NASCENCE/mecobo/EMServer/bin/77ac0f1f-8d66-4bb2-870d-c3d88853328c.pdf

# PIN15

# PIN14

# PIN13

# PIN12

# PIN11

# PIN10

# PIN09

# PIN08

# PIN07

# PIN06

# PIN05

# PIN04

# PIN02

# PIN01

# PIN00

CONSTANT 1V

CONSTANT 1V

CONSTANT 1V

CONSTANT 1V

CONSTANT 1V

CONSTANT 1V

CONSTANT 1V

CONSTANT 1V

CONSTANT 1V

CONSTANT 1V

CONSTANT 1V

CONSTANT 1V

CONSTANT 1V

CONSTANT 1V

CONSTANT 1V

CONSTANT 1V

CONSTANT 1V

CONSTANT 1V

CONSTANT 1V

CONSTANT 1V

CONSTANT 1V

CONSTANT 1V

CONSTANT 1V

CONSTANT 1V

CONSTANT 1V

CONSTANT 1V

CONSTANT 1V

CONSTANT 1V

CONSTANT 1V

CONSTANT 1V

CONSTANT 44V

CONSTANT 44V

CONSTANT 44V

CONSTANT 44V

CONSTANT 44V

CONSTANT 44V

CONSTANT 44V

CONSTANT 44V

CONSTANT 44V

CONSTANT 44V

CONSTANT 44V

CONSTANT 44V

CONSTANT 44V

CONSTANT 44V

CONSTANT 44V

CONSTANT 156V

CONSTANT 156V

CONSTANT 156V

CONSTANT 156V

CONSTANT 156V

CONSTANT 156V

CONSTANT 156V

CONSTANT 156V

CONSTANT 156V

CONSTANT 156V

CONSTANT 156V

CONSTANT 156V

CONSTANT 156V

CONSTANT 156V

CONSTANT 156V

CONSTANT 68V

CONSTANT 68V

CONSTANT 68V

CONSTANT 68V

CONSTANT 68V

CONSTANT 68V

CONSTANT 68V

CONSTANT 68V

CONSTANT 68V

CONSTANT 68V

CONSTANT 68V

CONSTANT 68V

CONSTANT 68V

CONSTANT 68V

CONSTANT 68V

CONSTANT 34V

CONSTANT 34V

CONSTANT 34V

CONSTANT 34V

CONSTANT 34V

CONSTANT 34V

CONSTANT 34V

CONSTANT 34V

CONSTANT 34V

CONSTANT 34V

CONSTANT 34V

CONSTANT 34V

CONSTANT 34V

CONSTANT 34V

CONSTANT 34V

CONSTANT 4V

CONSTANT 4V

CONSTANT 4V

CONSTANT 4V

CONSTANT 4V

CONSTANT 4V

CONSTANT 4V

CONSTANT 4V

CONSTANT 4V

CONSTANT 4V

CONSTANT 4V

CONSTANT 4V

CONSTANT 4V

CONSTANT 4V

CONSTANT 4V

RECORD

RECORD

RECORD

RECORD

RECORD

RECORD

RECORD

RECORD

RECORD

RECORD

RECORD

RECORD

RECORD

RECORD

RECORD
