NASCENCE/mecobo/EMServer/bin/7c396e15-6470-4e9b-a8e9-4cceba5d37cf.pdf

# PIN15

# PIN14

# PIN13

# PIN12

# PIN11

# PIN10

# PIN09

# PIN08

# PIN07

# PIN06

# PIN05

# PIN04

# PIN02

# PIN01

# PIN00

CONSTANT 255V

CONSTANT 255V

CONSTANT 255V

CONSTANT 255V

CONSTANT 255V

CONSTANT 255V

CONSTANT 255V

CONSTANT 255V

CONSTANT 255V

CONSTANT 255V

CONSTANT 255V

CONSTANT 255V

CONSTANT 255V

CONSTANT 255V

CONSTANT 255V

CONSTANT 255V

CONSTANT 255V

CONSTANT 255V

CONSTANT 255V

CONSTANT 255V

CONSTANT 255V

CONSTANT 255V

CONSTANT 255V

CONSTANT 255V

CONSTANT 255V

CONSTANT 255V

CONSTANT 255V

CONSTANT 255V

CONSTANT 255V

CONSTANT 255V

CONSTANT 53V

CONSTANT 53V

CONSTANT 53V

CONSTANT 53V

CONSTANT 53V

CONSTANT 53V

CONSTANT 53V

CONSTANT 53V

CONSTANT 53V

CONSTANT 53V

CONSTANT 53V

CONSTANT 53V

CONSTANT 53V

CONSTANT 53V

CONSTANT 53V

CONSTANT 8V

CONSTANT 8V

CONSTANT 8V

CONSTANT 8V

CONSTANT 8V

CONSTANT 8V

CONSTANT 8V

CONSTANT 8V

CONSTANT 8V

CONSTANT 8V

CONSTANT 8V

CONSTANT 8V

CONSTANT 8V

CONSTANT 8V

CONSTANT 8V

CONSTANT 240V

CONSTANT 240V

CONSTANT 240V

CONSTANT 240V

CONSTANT 240V

CONSTANT 240V

CONSTANT 240V

CONSTANT 240V

CONSTANT 240V

CONSTANT 240V

CONSTANT 240V

CONSTANT 240V

CONSTANT 240V

CONSTANT 240V

CONSTANT 240V

CONSTANT 153V

CONSTANT 153V

CONSTANT 153V

CONSTANT 153V

CONSTANT 153V

CONSTANT 153V

CONSTANT 153V

CONSTANT 153V

CONSTANT 153V

CONSTANT 153V

CONSTANT 153V

CONSTANT 153V

CONSTANT 153V

CONSTANT 153V

CONSTANT 153V

CONSTANT 51V

CONSTANT 51V

CONSTANT 51V

CONSTANT 51V

CONSTANT 51V

CONSTANT 51V

CONSTANT 51V

CONSTANT 51V

CONSTANT 51V

CONSTANT 51V

CONSTANT 51V

CONSTANT 51V

CONSTANT 51V

CONSTANT 51V

CONSTANT 51V

RECORD

RECORD

RECORD

RECORD

RECORD

RECORD

RECORD

RECORD

RECORD

RECORD

RECORD

RECORD

RECORD

RECORD

RECORD
