NASCENCE/mecobo/EMServer/bin/827bd61a-1e40-4bb6-a9ad-a4c73b333c4b.pdf

# PIN15

# PIN14

# PIN13

# PIN12

# PIN11

# PIN10

# PIN09

# PIN08

# PIN07

# PIN06

# PIN05

# PIN04

# PIN02

# PIN01

# PIN00

CONSTANT 1V

CONSTANT 1V

CONSTANT 1V

CONSTANT 1V

CONSTANT 1V

CONSTANT 1V

CONSTANT 1V

CONSTANT 1V

CONSTANT 1V

CONSTANT 1V

CONSTANT 1V

CONSTANT 1V

CONSTANT 1V

CONSTANT 1V

CONSTANT 1V

CONSTANT 255V

CONSTANT 255V

CONSTANT 255V

CONSTANT 255V

CONSTANT 255V

CONSTANT 255V

CONSTANT 255V

CONSTANT 255V

CONSTANT 255V

CONSTANT 255V

CONSTANT 255V

CONSTANT 255V

CONSTANT 255V

CONSTANT 255V

CONSTANT 255V

CONSTANT 51V

CONSTANT 51V

CONSTANT 51V

CONSTANT 51V

CONSTANT 51V

CONSTANT 51V

CONSTANT 51V

CONSTANT 51V

CONSTANT 51V

CONSTANT 51V

CONSTANT 51V

CONSTANT 51V

CONSTANT 51V

CONSTANT 51V

CONSTANT 51V

CONSTANT 217V

CONSTANT 217V

CONSTANT 217V

CONSTANT 217V

CONSTANT 217V

CONSTANT 217V

CONSTANT 217V

CONSTANT 217V

CONSTANT 217V

CONSTANT 217V

CONSTANT 217V

CONSTANT 217V

CONSTANT 217V

CONSTANT 217V

CONSTANT 217V

CONSTANT 230V

CONSTANT 230V

CONSTANT 230V

CONSTANT 230V

CONSTANT 230V

CONSTANT 230V

CONSTANT 230V

CONSTANT 230V

CONSTANT 230V

CONSTANT 230V

CONSTANT 230V

CONSTANT 230V

CONSTANT 230V

CONSTANT 230V

CONSTANT 230V

CONSTANT 61V

CONSTANT 61V

CONSTANT 61V

CONSTANT 61V

CONSTANT 61V

CONSTANT 61V

CONSTANT 61V

CONSTANT 61V

CONSTANT 61V

CONSTANT 61V

CONSTANT 61V

CONSTANT 61V

CONSTANT 61V

CONSTANT 61V

CONSTANT 61V

CONSTANT 178V

CONSTANT 178V

CONSTANT 178V

CONSTANT 178V

CONSTANT 178V

CONSTANT 178V

CONSTANT 178V

CONSTANT 178V

CONSTANT 178V

CONSTANT 178V

CONSTANT 178V

CONSTANT 178V

CONSTANT 178V

CONSTANT 178V

CONSTANT 178V

RECORD

RECORD

RECORD

RECORD

RECORD

RECORD

RECORD

RECORD

RECORD

RECORD

RECORD

RECORD

RECORD

RECORD

RECORD
