NASCENCE/mecobo/EMServer/bin/a4c77bfb-b747-4d07-bfa7-c140843181cd.pdf

# PIN15

# PIN13

# PIN12

# PIN10

# PIN08

# PIN06

# PIN05

# PIN01

CONSTANT 1V

CONSTANT 1V

CONSTANT 1V

CONSTANT 1V

CONSTANT 255V

CONSTANT 255V

CONSTANT 255V

CONSTANT 255V

CONSTANT 212V

CONSTANT 212V

CONSTANT 212V

CONSTANT 212V

CONSTANT 243V

CONSTANT 243V

CONSTANT 243V

CONSTANT 243V

CONSTANT 125V

CONSTANT 125V

CONSTANT 125V

CONSTANT 125V

CONSTANT 35V

CONSTANT 35V

CONSTANT 35V

CONSTANT 35V

CONSTANT 128V

CONSTANT 128V

CONSTANT 128V

CONSTANT 128V

RECORD

RECORD

RECORD

RECORD
