NASCENCE/mecobo/EMServer/bin/a68f7f57-0318-45c7-98cb-ac7f5dc991e0.pdf

# PIN15

# PIN14

# PIN13

# PIN11

# PIN10

# PIN05

# PIN04

# PIN02

CONSTANT 1V

CONSTANT 1V

CONSTANT 1V

CONSTANT 1V

CONSTANT 1V

CONSTANT 1V

CONSTANT 94V

CONSTANT 94V

CONSTANT 94V

CONSTANT 212V

CONSTANT 212V

CONSTANT 212V

CONSTANT 108V

CONSTANT 108V

CONSTANT 108V

CONSTANT 62V

CONSTANT 62V

CONSTANT 62V

CONSTANT 214V

CONSTANT 214V

CONSTANT 214V

RECORD

RECORD

RECORD
