NASCENCE/mecobo/EMServer/bin/b2d921c1-c7bb-4e98-b5ac-985218d47814.pdf

# PIN15

# PIN14

# PIN13

# PIN12

# PIN11

# PIN10

# PIN09

# PIN08

# PIN07

# PIN06

# PIN05

# PIN04

# PIN02

# PIN01

# PIN00

CONSTANT 255V

CONSTANT 255V

CONSTANT 255V

CONSTANT 255V

CONSTANT 255V

CONSTANT 255V

CONSTANT 255V

CONSTANT 255V

CONSTANT 255V

CONSTANT 255V

CONSTANT 255V

CONSTANT 255V

CONSTANT 255V

CONSTANT 255V

CONSTANT 255V

CONSTANT 255V

CONSTANT 255V

CONSTANT 255V

CONSTANT 255V

CONSTANT 255V

CONSTANT 255V

CONSTANT 255V

CONSTANT 255V

CONSTANT 255V

CONSTANT 255V

CONSTANT 255V

CONSTANT 255V

CONSTANT 255V

CONSTANT 255V

CONSTANT 255V

CONSTANT 39V

CONSTANT 39V

CONSTANT 39V

CONSTANT 39V

CONSTANT 39V

CONSTANT 39V

CONSTANT 39V

CONSTANT 39V

CONSTANT 39V

CONSTANT 39V

CONSTANT 39V

CONSTANT 39V

CONSTANT 39V

CONSTANT 39V

CONSTANT 39V

CONSTANT 171V

CONSTANT 171V

CONSTANT 171V

CONSTANT 171V

CONSTANT 171V

CONSTANT 171V

CONSTANT 171V

CONSTANT 171V

CONSTANT 171V

CONSTANT 171V

CONSTANT 171V

CONSTANT 171V

CONSTANT 171V

CONSTANT 171V

CONSTANT 171V

CONSTANT 53V

CONSTANT 53V

CONSTANT 53V

CONSTANT 53V

CONSTANT 53V

CONSTANT 53V

CONSTANT 53V

CONSTANT 53V

CONSTANT 53V

CONSTANT 53V

CONSTANT 53V

CONSTANT 53V

CONSTANT 53V

CONSTANT 53V

CONSTANT 53V

CONSTANT 181V

CONSTANT 181V

CONSTANT 181V

CONSTANT 181V

CONSTANT 181V

CONSTANT 181V

CONSTANT 181V

CONSTANT 181V

CONSTANT 181V

CONSTANT 181V

CONSTANT 181V

CONSTANT 181V

CONSTANT 181V

CONSTANT 181V

CONSTANT 181V

CONSTANT 83V

CONSTANT 83V

CONSTANT 83V

CONSTANT 83V

CONSTANT 83V

CONSTANT 83V

CONSTANT 83V

CONSTANT 83V

CONSTANT 83V

CONSTANT 83V

CONSTANT 83V

CONSTANT 83V

CONSTANT 83V

CONSTANT 83V

CONSTANT 83V

RECORD

RECORD

RECORD

RECORD

RECORD

RECORD

RECORD

RECORD

RECORD

RECORD

RECORD

RECORD

RECORD

RECORD

RECORD
