NASCENCE/mecobo/EMServer/bin/bf1b4498-306a-4170-b79d-7af4890ea45a.pdf

# PIN14

# PIN11

# PIN09

# PIN06

# PIN05

# PIN04

# PIN02

# PIN01

CONSTANT 255V

CONSTANT 255V

CONSTANT 255V

CONSTANT 255V

CONSTANT 255V

CONSTANT 255V

CONSTANT 255V

CONSTANT 255V

CONSTANT 255V

CONSTANT 255V

CONSTANT 200V

CONSTANT 200V

CONSTANT 200V

CONSTANT 200V

CONSTANT 200V

CONSTANT 249V

CONSTANT 249V

CONSTANT 249V

CONSTANT 249V

CONSTANT 249V

CONSTANT 137V

CONSTANT 137V

CONSTANT 137V

CONSTANT 137V

CONSTANT 137V

CONSTANT 69V

CONSTANT 69V

CONSTANT 69V

CONSTANT 69V

CONSTANT 69V

CONSTANT 124V

CONSTANT 124V

CONSTANT 124V

CONSTANT 124V

CONSTANT 124V

RECORD

RECORD

RECORD

RECORD

RECORD
