NASCENCE/mecobo/EMServer/bin/ced6a055-62d8-4b0a-8d0b-5f8a17def5bb.pdf

# PIN15

# PIN14

# PIN13

# PIN12

# PIN11

# PIN10

# PIN09

# PIN08

# PIN07

# PIN06

# PIN05

# PIN04

# PIN02

# PIN01

# PIN00

CONSTANT 255V

CONSTANT 255V

CONSTANT 255V

CONSTANT 255V

CONSTANT 255V

CONSTANT 255V

CONSTANT 255V

CONSTANT 255V

CONSTANT 255V

CONSTANT 255V

CONSTANT 255V

CONSTANT 255V

CONSTANT 255V

CONSTANT 255V

CONSTANT 255V

CONSTANT 1V

CONSTANT 1V

CONSTANT 1V

CONSTANT 1V

CONSTANT 1V

CONSTANT 1V

CONSTANT 1V

CONSTANT 1V

CONSTANT 1V

CONSTANT 1V

CONSTANT 1V

CONSTANT 1V

CONSTANT 1V

CONSTANT 1V

CONSTANT 1V

CONSTANT 218V

CONSTANT 218V

CONSTANT 218V

CONSTANT 218V

CONSTANT 218V

CONSTANT 218V

CONSTANT 218V

CONSTANT 218V

CONSTANT 218V

CONSTANT 218V

CONSTANT 218V

CONSTANT 218V

CONSTANT 218V

CONSTANT 218V

CONSTANT 218V

CONSTANT 8V

CONSTANT 8V

CONSTANT 8V

CONSTANT 8V

CONSTANT 8V

CONSTANT 8V

CONSTANT 8V

CONSTANT 8V

CONSTANT 8V

CONSTANT 8V

CONSTANT 8V

CONSTANT 8V

CONSTANT 8V

CONSTANT 8V

CONSTANT 8V

CONSTANT 49V

CONSTANT 49V

CONSTANT 49V

CONSTANT 49V

CONSTANT 49V

CONSTANT 49V

CONSTANT 49V

CONSTANT 49V

CONSTANT 49V

CONSTANT 49V

CONSTANT 49V

CONSTANT 49V

CONSTANT 49V

CONSTANT 49V

CONSTANT 49V

CONSTANT 214V

CONSTANT 214V

CONSTANT 214V

CONSTANT 214V

CONSTANT 214V

CONSTANT 214V

CONSTANT 214V

CONSTANT 214V

CONSTANT 214V

CONSTANT 214V

CONSTANT 214V

CONSTANT 214V

CONSTANT 214V

CONSTANT 214V

CONSTANT 214V

CONSTANT 128V

CONSTANT 128V

CONSTANT 128V

CONSTANT 128V

CONSTANT 128V

CONSTANT 128V

CONSTANT 128V

CONSTANT 128V

CONSTANT 128V

CONSTANT 128V

CONSTANT 128V

CONSTANT 128V

CONSTANT 128V

CONSTANT 128V

CONSTANT 128V

RECORD

RECORD

RECORD

RECORD

RECORD

RECORD

RECORD

RECORD

RECORD

RECORD

RECORD

RECORD

RECORD

RECORD

RECORD
