NASCENCE/mecobo/EMServer/bin/d15176d1-3dd1-42c1-ac68-71cac9abdab1.pdf

# PIN13

# PIN12

# PIN11

# PIN10

# PIN08

# PIN06

# PIN04

# PIN00

CONSTANT 1V

CONSTANT 1V

CONSTANT 1V

CONSTANT 1V

CONSTANT 1V

CONSTANT 1V

CONSTANT 1V

CONSTANT 1V

CONSTANT 99V

CONSTANT 99V

CONSTANT 99V

CONSTANT 99V

CONSTANT 72V

CONSTANT 72V

CONSTANT 72V

CONSTANT 72V

CONSTANT 144V

CONSTANT 144V

CONSTANT 144V

CONSTANT 144V

CONSTANT 234V

CONSTANT 234V

CONSTANT 234V

CONSTANT 234V

CONSTANT 242V

CONSTANT 242V

CONSTANT 242V

CONSTANT 242V

RECORD

RECORD

RECORD

RECORD
