NASCENCE/mecobo/EMServer/bin/ed7d3c6d-ea88-4af1-b51c-1e0c0bd52c95.pdf

# PIN15

# PIN14

# PIN13

# PIN12

# PIN11

# PIN10

# PIN09

# PIN08

# PIN07

# PIN06

# PIN05

# PIN04

# PIN02

# PIN01

# PIN00

CONSTANT 1V

CONSTANT 1V

CONSTANT 1V

CONSTANT 1V

CONSTANT 1V

CONSTANT 1V

CONSTANT 1V

CONSTANT 1V

CONSTANT 1V

CONSTANT 1V

CONSTANT 1V

CONSTANT 1V

CONSTANT 1V

CONSTANT 1V

CONSTANT 1V

CONSTANT 255V

CONSTANT 255V

CONSTANT 255V

CONSTANT 255V

CONSTANT 255V

CONSTANT 255V

CONSTANT 255V

CONSTANT 255V

CONSTANT 255V

CONSTANT 255V

CONSTANT 255V

CONSTANT 255V

CONSTANT 255V

CONSTANT 255V

CONSTANT 255V

CONSTANT 16V

CONSTANT 16V

CONSTANT 16V

CONSTANT 16V

CONSTANT 16V

CONSTANT 16V

CONSTANT 16V

CONSTANT 16V

CONSTANT 16V

CONSTANT 16V

CONSTANT 16V

CONSTANT 16V

CONSTANT 16V

CONSTANT 16V

CONSTANT 16V

CONSTANT 196V

CONSTANT 196V

CONSTANT 196V

CONSTANT 196V

CONSTANT 196V

CONSTANT 196V

CONSTANT 196V

CONSTANT 196V

CONSTANT 196V

CONSTANT 196V

CONSTANT 196V

CONSTANT 196V

CONSTANT 196V

CONSTANT 196V

CONSTANT 196V

CONSTANT 141V

CONSTANT 141V

CONSTANT 141V

CONSTANT 141V

CONSTANT 141V

CONSTANT 141V

CONSTANT 141V

CONSTANT 141V

CONSTANT 141V

CONSTANT 141V

CONSTANT 141V

CONSTANT 141V

CONSTANT 141V

CONSTANT 141V

CONSTANT 141V

CONSTANT 252V

CONSTANT 252V

CONSTANT 252V

CONSTANT 252V

CONSTANT 252V

CONSTANT 252V

CONSTANT 252V

CONSTANT 252V

CONSTANT 252V

CONSTANT 252V

CONSTANT 252V

CONSTANT 252V

CONSTANT 252V

CONSTANT 252V

CONSTANT 252V

CONSTANT 155V

CONSTANT 155V

CONSTANT 155V

CONSTANT 155V

CONSTANT 155V

CONSTANT 155V

CONSTANT 155V

CONSTANT 155V

CONSTANT 155V

CONSTANT 155V

CONSTANT 155V

CONSTANT 155V

CONSTANT 155V

CONSTANT 155V

CONSTANT 155V

RECORD

RECORD

RECORD

RECORD

RECORD

RECORD

RECORD

RECORD

RECORD

RECORD

RECORD

RECORD

RECORD

RECORD

RECORD
