NASCENCE/mecobo/EMServer/bin/fe45399b-97a2-48f1-b828-bda7ee56db6b.pdf

# PIN15

# PIN14

# PIN13

# PIN12

# PIN11

# PIN10

# PIN09

# PIN08

# PIN07

# PIN06

# PIN05

# PIN04

# PIN02

# PIN01

# PIN00

CONSTANT 1V

CONSTANT 1V

CONSTANT 1V

CONSTANT 1V

CONSTANT 1V

CONSTANT 1V

CONSTANT 1V

CONSTANT 1V

CONSTANT 1V

CONSTANT 1V

CONSTANT 1V

CONSTANT 1V

CONSTANT 1V

CONSTANT 1V

CONSTANT 1V

CONSTANT 255V

CONSTANT 255V

CONSTANT 255V

CONSTANT 255V

CONSTANT 255V

CONSTANT 255V

CONSTANT 255V

CONSTANT 255V

CONSTANT 255V

CONSTANT 255V

CONSTANT 255V

CONSTANT 255V

CONSTANT 255V

CONSTANT 255V

CONSTANT 255V

CONSTANT 97V

CONSTANT 97V

CONSTANT 97V

CONSTANT 97V

CONSTANT 97V

CONSTANT 97V

CONSTANT 97V

CONSTANT 97V

CONSTANT 97V

CONSTANT 97V

CONSTANT 97V

CONSTANT 97V

CONSTANT 97V

CONSTANT 97V

CONSTANT 97V

CONSTANT 104V

CONSTANT 104V

CONSTANT 104V

CONSTANT 104V

CONSTANT 104V

CONSTANT 104V

CONSTANT 104V

CONSTANT 104V

CONSTANT 104V

CONSTANT 104V

CONSTANT 104V

CONSTANT 104V

CONSTANT 104V

CONSTANT 104V

CONSTANT 104V

CONSTANT 75V

CONSTANT 75V

CONSTANT 75V

CONSTANT 75V

CONSTANT 75V

CONSTANT 75V

CONSTANT 75V

CONSTANT 75V

CONSTANT 75V

CONSTANT 75V

CONSTANT 75V

CONSTANT 75V

CONSTANT 75V

CONSTANT 75V

CONSTANT 75V

CONSTANT 244V

CONSTANT 244V

CONSTANT 244V

CONSTANT 244V

CONSTANT 244V

CONSTANT 244V

CONSTANT 244V

CONSTANT 244V

CONSTANT 244V

CONSTANT 244V

CONSTANT 244V

CONSTANT 244V

CONSTANT 244V

CONSTANT 244V

CONSTANT 244V

CONSTANT 180V

CONSTANT 180V

CONSTANT 180V

CONSTANT 180V

CONSTANT 180V

CONSTANT 180V

CONSTANT 180V

CONSTANT 180V

CONSTANT 180V

CONSTANT 180V

CONSTANT 180V

CONSTANT 180V

CONSTANT 180V

CONSTANT 180V

CONSTANT 180V

RECORD

RECORD

RECORD

RECORD

RECORD

RECORD

RECORD

RECORD

RECORD

RECORD

RECORD

RECORD

RECORD

RECORD

RECORD
