NASCENCE/mecobo/EMServer/bin/ffceb596-d40d-4249-89b4-cb11e576af7a.pdf

# PIN15

# PIN14

# PIN13

# PIN12

# PIN11

# PIN10

# PIN09

# PIN08

# PIN07

# PIN06

# PIN05

# PIN04

# PIN02

# PIN01

# PIN00

CONSTANT 1V

CONSTANT 1V

CONSTANT 1V

CONSTANT 1V

CONSTANT 1V

CONSTANT 1V

CONSTANT 1V

CONSTANT 1V

CONSTANT 1V

CONSTANT 1V

CONSTANT 1V

CONSTANT 1V

CONSTANT 1V

CONSTANT 1V

CONSTANT 1V

CONSTANT 255V

CONSTANT 255V

CONSTANT 255V

CONSTANT 255V

CONSTANT 255V

CONSTANT 255V

CONSTANT 255V

CONSTANT 255V

CONSTANT 255V

CONSTANT 255V

CONSTANT 255V

CONSTANT 255V

CONSTANT 255V

CONSTANT 255V

CONSTANT 255V

CONSTANT 114V

CONSTANT 114V

CONSTANT 114V

CONSTANT 114V

CONSTANT 114V

CONSTANT 114V

CONSTANT 114V

CONSTANT 114V

CONSTANT 114V

CONSTANT 114V

CONSTANT 114V

CONSTANT 114V

CONSTANT 114V

CONSTANT 114V

CONSTANT 114V

CONSTANT 225V

CONSTANT 225V

CONSTANT 225V

CONSTANT 225V

CONSTANT 225V

CONSTANT 225V

CONSTANT 225V

CONSTANT 225V

CONSTANT 225V

CONSTANT 225V

CONSTANT 225V

CONSTANT 225V

CONSTANT 225V

CONSTANT 225V

CONSTANT 225V

CONSTANT 222V

CONSTANT 222V

CONSTANT 222V

CONSTANT 222V

CONSTANT 222V

CONSTANT 222V

CONSTANT 222V

CONSTANT 222V

CONSTANT 222V

CONSTANT 222V

CONSTANT 222V

CONSTANT 222V

CONSTANT 222V

CONSTANT 222V

CONSTANT 222V

CONSTANT 6V

CONSTANT 6V

CONSTANT 6V

CONSTANT 6V

CONSTANT 6V

CONSTANT 6V

CONSTANT 6V

CONSTANT 6V

CONSTANT 6V

CONSTANT 6V

CONSTANT 6V

CONSTANT 6V

CONSTANT 6V

CONSTANT 6V

CONSTANT 6V

CONSTANT 66V

CONSTANT 66V

CONSTANT 66V

CONSTANT 66V

CONSTANT 66V

CONSTANT 66V

CONSTANT 66V

CONSTANT 66V

CONSTANT 66V

CONSTANT 66V

CONSTANT 66V

CONSTANT 66V

CONSTANT 66V

CONSTANT 66V

CONSTANT 66V

RECORD

RECORD

RECORD

RECORD

RECORD

RECORD

RECORD

RECORD

RECORD

RECORD

RECORD

RECORD

RECORD

RECORD

RECORD
