NASCENCE/mecobo/EMServer/bin/LogServer/Gates_20140802_155137/20140802_155140515_CONFIG.txt

{
  "Sequence": {
    "SequenceItem0": {
      "Pin0": "10",
      "Amp": "1",
      "CT": "0",
      "End": "128",
      "Str": "0",
      "Fre": "0",
      "Opt": "CONSTANT",
      "Pha": "0",
      "VSR": "-1",
      "WFT": "-1",
      "Wav": "PWM"
    },
    "SequenceItem1": {
      "Pin0": "1",
      "Amp": "0",
      "CT": "0",
      "End": "128",
      "Str": "0",
      "Fre": "0",
      "Opt": "CONSTANT",
      "Pha": "0",
      "VSR": "-1",
      "WFT": "-1",
      "Wav": "PWM"
    },
    "SequenceItem2": {
      "Pin0": "10",
      "Amp": "0",
      "CT": "0",
      "End": "129",
      "Str": "128",
      "Fre": "0",
      "Opt": "emNULL",
      "Pha": "0",
      "VSR": "-1",
      "WFT": "-1",
      "Wav": "emNULL"
    },
    "SequenceItem3": {
      "Pin0": "2",
      "Amp": "0",
      "CT": "50",
      "End": "128",
      "Str": "0",
      "Fre": "4711",
      "Opt": "CONSTANT",
      "Pha": "8",
      "VSR": "-1",
      "WFT": "-1",
      "Wav": "PWM"
    },
    "SequenceItem4": {
      "Pin0": "9",
      "Amp": "1",
      "CT": "50",
      "End": "128",
      "Str": "0",
      "Fre": "9692",
      "Opt": "CONSTANT",
      "Pha": "1",
      "VSR": "-1",
      "WFT": "-1",
      "Wav": "PWM"
    },
    "SequenceItem5": {
      "Pin0": "5",
      "Amp": "0",
      "CT": "50",
      "End": "128",
      "Str": "0",
      "Fre": "1573",
      "Opt": "CONSTANT",
      "Pha": "5",
      "VSR": "-1",
      "WFT": "-1",
      "Wav": "PWM"
    },
    "SequenceItem6": {
      "Pin0": "0",
      "Amp": "0",
      "CT": "50",
      "End": "128",
      "Str": "0",
      "Fre": "5389",
      "Opt": "CONSTANT",
      "Pha": "5",
      "VSR": "-1",
      "WFT": "-1",
      "Wav": "PWM"
    },
    "SequenceItem7": {
      "Pin0": "11",
      "Amp": "1",
      "CT": "50",
      "End": "128",
      "Str": "0",
      "Fre": "5615",
      "Opt": "CONSTANT",
      "Pha": "2",
      "VSR": "-1",
      "WFT": "-1",
      "Wav": "PWM"
    },
    "SequenceItem8": {
      "Pin0": "6",
      "Amp": "0",
      "CT": "50",
      "End": "128",
      "Str": "0",
      "Fre": "7958",
      "Opt": "CONSTANT",
      "Pha": "3",
      "VSR": "-1",
      "WFT": "-1",
      "Wav": "PWM"
    },
    "SequenceItem9": {
      "Pin0": "3",
      "Amp": "0",
      "CT": "50",
      "End": "128",
      "Str": "0",
      "Fre": "9643",
      "Opt": "CONSTANT",
      "Pha": "7",
      "VSR": "-1",
      "WFT": "-1",
      "Wav": "PWM"
    },
    "SequenceItem10": {
      "Pin0": "7",
      "Amp": "0",
      "CT": "50",
      "End": "128",
      "Str": "0",
      "Fre": "6909",
      "Opt": "CONSTANT",
      "Pha": "3",
      "VSR": "-1",
      "WFT": "-1",
      "Wav": "PWM"
    },
    "SequenceItem11": {
      "Pin0": "8",
      "Amp": "0",
      "CT": "0",
      "End": "128",
      "Str": "0",
      "Fre": "5000",
      "Opt": "RECORD",
      "Pha": "0",
      "VSR": "-1",
      "WFT": "-1",
      "Wav": "emNULL"
    }
  },
  "Results": {
    "Case 0": " TESTCASE 0  True ,False=>True  False FAIL",
    "Case 1": " TESTCASE 1  False,True =>True  False FAIL",
    "Case 2": " TESTCASE 2  True ,True =>False False PASS",
    "Case 3": " TESTCASE 3  False,False=>True  False FAIL",
    "Case 4": " TESTCASE 4  True ,False=>True  False FAIL",
    "Case 5": " TESTCASE 5  False,False=>True  False FAIL",
    "Case 6": " TESTCASE 6  True ,True =>False False PASS",
    "Case 7": " TESTCASE 7  False,True =>True  False FAIL",
    "Case 8": " TESTCASE 8  False,True =>True  False FAIL",
    "Case 9": " TESTCASE 9  True ,False=>True  False FAIL",
    "Case 10": " TESTCASE 10 True ,True =>False False PASS",
    "Case 11": " TESTCASE 11 False,False=>True  False FAIL",
    "Case 12": " TESTCASE 12 False,False=>True  False FAIL",
    "Case 13": " TESTCASE 13 True ,True =>False False PASS",
    "Case 14": " TESTCASE 14 True ,False=>True  False FAIL",
    "Case 15": " TESTCASE 15 False,True =>True  False FAIL"
  },
  "Fitness": {
    "Score": "0.25",
    "Evaluation index": "0"
  }
}
