NASCENCE/mecobo/fpga/main_clocks_mmcm/main_clocks.v

// file: main_clocks.v
// 
// (c) Copyright 2008 - 2011 Xilinx, Inc. All rights reserved.
// 
// This file contains confidential and proprietary information
// of Xilinx, Inc. and is protected under U.S. and
// international copyright and other intellectual property
// laws.
// 
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
// CRITICAL APPLICATIONS
// Xilinx products are not designed or intended to be fail-
// safe, or for use in any application requiring fail-safe
// performance, such as life-support or safety devices or
// systems, Class III medical devices, nuclear facilities,
// applications related to the deployment of airbags, or any
// other applications that could lead to death, personal
// injury, or severe property or environmental damage
// (individually and collectively, "Critical
// Applications"). Customer assumes the sole risk and
// liability of any use of Xilinx products in Critical
// Applications, subject only to applicable laws and
// regulations governing limitations on product liability.
// 
// THIS COPYRIGHT NOTICE AND DISCLAIMER MUST BE RETAINED AS
// PART OF THIS FILE AT ALL TIMES.
// 
//----------------------------------------------------------------------------
// User entered comments
//----------------------------------------------------------------------------
// None
//
//----------------------------------------------------------------------------
// "Output    Output      Phase     Duty      Pk-to-Pk        Phase"
// "Clock    Freq (MHz) (degrees) Cycle (%) Jitter (ps)  Error (ps)"
//----------------------------------------------------------------------------
// CLK_OUT1____75.000______0.000______50.0______248.869____240.171
// CLK_OUT2_____5.000______0.000______50.0______430.859____240.171
// CLK_OUT3____10.000______0.000______50.0______376.111____240.171
// CLK_OUT4____30.000______0.000______50.0______301.291____240.171
//
//----------------------------------------------------------------------------
// "Input Clock   Freq (MHz)    Input Jitter (UI)"
//----------------------------------------------------------------------------
// __primary__________50.000____________0.010

`timescale 1ps/1ps

(* CORE_GENERATION_INFO = "main_clocks,clk_wiz_v3_6,{component_name=main_clocks,use_phase_alignment=true,use_min_o_jitter=false,use_max_i_jitter=false,use_dyn_phase_shift=false,use_inclk_switchover=false,use_dyn_reconfig=false,feedback_source=FDBK_AUTO,primtype_sel=PLL_BASE,num_out_clk=4,clkin1_period=20.000,clkin2_period=20.000,use_power_down=false,use_reset=true,use_locked=true,use_inclk_stopped=false,use_status=false,use_freeze=false,use_clk_valid=false,feedback_type=SINGLE,clock_mgr_type=AUTO,manual_override=false}" *)
module main_clocks
 (// Clock in ports
  input         CLK_IN1,
  // Clock out ports
  output        CLK_OUT_75,
  output        CLK_OUT_5,
  output        CLK_OUT_10,
  output        CLK_OUT_30,
  // Status and control signals
  input         RESET,
  output        LOCKED
 );

  // Input buffering
  //------------------------------------
  IBUFG clkin1_buf
   (.O (clkin1),
    .I (CLK_IN1));


  // Clocking primitive
  //------------------------------------
  // Instantiation of the PLL primitive
  //    * Unused inputs are tied off
  //    * Unused outputs are labeled unused
  wire [15:0] do_unused;
  wire        drdy_unused;
  wire        clkfbout;
  wire        clkfbout_buf;
  wire        clkout4_unused;
  wire        clkout5_unused;

  PLL_BASE
  #(.BANDWIDTH              ("OPTIMIZED"),
    .CLK_FEEDBACK           ("CLKFBOUT"),
    .COMPENSATION           ("SYSTEM_SYNCHRONOUS"),
    .DIVCLK_DIVIDE          (1),
    .CLKFBOUT_MULT          (9),
    .CLKFBOUT_PHASE         (0.000),
    .CLKOUT0_DIVIDE         (6),
    .CLKOUT0_PHASE          (0.000),
    .CLKOUT0_DUTY_CYCLE     (0.500),
    .CLKOUT1_DIVIDE         (90),
    .CLKOUT1_PHASE          (0.000),
    .CLKOUT1_DUTY_CYCLE     (0.500),
    .CLKOUT2_DIVIDE         (45),
    .CLKOUT2_PHASE          (0.000),
    .CLKOUT2_DUTY_CYCLE     (0.500),
    .CLKOUT3_DIVIDE         (15),
    .CLKOUT3_PHASE          (0.000),
    .CLKOUT3_DUTY_CYCLE     (0.500),
    .CLKIN_PERIOD           (20.000),
    .REF_JITTER             (0.010))
  pll_base_inst
    // Output clocks
   (.CLKFBOUT              (clkfbout),
    .CLKOUT0               (clkout0),
    .CLKOUT1               (clkout1),
    .CLKOUT2               (clkout2),
    .CLKOUT3               (clkout3),
    .CLKOUT4               (clkout4_unused),
    .CLKOUT5               (clkout5_unused),
    // Status and control signals
    .LOCKED                (LOCKED),
    .RST                   (RESET),
     // Input clock control
    .CLKFBIN               (clkfbout_buf),
    .CLKIN                 (clkin1));


  // Output buffering
  //-----------------------------------
  BUFG clkf_buf
   (.O (clkfbout_buf),
    .I (clkfbout));

  BUFG clkout1_buf
   (.O   (CLK_OUT_75),
    .I   (clkout0));


  BUFG clkout2_buf
   (.O   (CLK_OUT_5),
    .I   (clkout1));

  BUFG clkout3_buf
   (.O   (CLK_OUT_10),
    .I   (clkout2));

  BUFG clkout4_buf
   (.O   (CLK_OUT_30),
    .I   (clkout3));



endmodule
