NASCENCE/mecobo/EMServer/bin/LogServer/Gates_20140802_155137/20140802_155158777_CONFIG.txt

{
  "Sequence": {
    "SequenceItem0": {
      "Pin0": "6",
      "Amp": "0",
      "CT": "0",
      "End": "128",
      "Str": "0",
      "Fre": "0",
      "Opt": "CONSTANT",
      "Pha": "0",
      "VSR": "-1",
      "WFT": "-1",
      "Wav": "PWM"
    },
    "SequenceItem1": {
      "Pin0": "3",
      "Amp": "1",
      "CT": "0",
      "End": "128",
      "Str": "0",
      "Fre": "0",
      "Opt": "CONSTANT",
      "Pha": "0",
      "VSR": "-1",
      "WFT": "-1",
      "Wav": "PWM"
    },
    "SequenceItem2": {
      "Pin0": "6",
      "Amp": "0",
      "CT": "0",
      "End": "129",
      "Str": "128",
      "Fre": "0",
      "Opt": "emNULL",
      "Pha": "0",
      "VSR": "-1",
      "WFT": "-1",
      "Wav": "emNULL"
    },
    "SequenceItem3": {
      "Pin0": "5",
      "Pin1": "1",
      "Amp": "0",
      "CT": "50",
      "End": "128",
      "Str": "0",
      "Fre": "4328",
      "Opt": "CONSTANT",
      "Pha": "4",
      "VSR": "-1",
      "WFT": "-1",
      "Wav": "PWM"
    },
    "SequenceItem4": {
      "Pin0": "7",
      "Pin1": "1",
      "Pin2": "7",
      "Pin3": "7",
      "Pin4": "7",
      "Amp": "1",
      "CT": "50",
      "End": "128",
      "Str": "0",
      "Fre": "4669",
      "Opt": "CONSTANT",
      "Pha": "7",
      "VSR": "-1",
      "WFT": "-1",
      "Wav": "PWM"
    },
    "SequenceItem5": {
      "Pin0": "4",
      "Pin1": "4",
      "Pin2": "4",
      "Pin3": "4",
      "Pin4": "4",
      "Amp": "0",
      "CT": "50",
      "End": "128",
      "Str": "0",
      "Fre": "4679",
      "Opt": "CONSTANT",
      "Pha": "8",
      "VSR": "-1",
      "WFT": "-1",
      "Wav": "PWM"
    },
    "SequenceItem6": {
      "Pin0": "0",
      "Amp": "1",
      "CT": "50",
      "End": "128",
      "Str": "0",
      "Fre": "8216",
      "Opt": "CONSTANT",
      "Pha": "4",
      "VSR": "-1",
      "WFT": "-1",
      "Wav": "PWM"
    },
    "SequenceItem7": {
      "Pin0": "2",
      "Pin1": "1",
      "Pin2": "2",
      "Amp": "0",
      "CT": "50",
      "End": "128",
      "Str": "0",
      "Fre": "8341",
      "Opt": "CONSTANT",
      "Pha": "7",
      "VSR": "-1",
      "WFT": "-1",
      "Wav": "PWM"
    },
    "SequenceItem8": {
      "Pin0": "9",
      "Pin1": "1",
      "Pin2": "9",
      "Pin3": "9",
      "Pin4": "9",
      "Amp": "0",
      "CT": "50",
      "End": "128",
      "Str": "0",
      "Fre": "4233",
      "Opt": "CONSTANT",
      "Pha": "2",
      "VSR": "-1",
      "WFT": "-1",
      "Wav": "PWM"
    },
    "SequenceItem9": {
      "Pin0": "10",
      "Pin1": "1",
      "Amp": "1",
      "CT": "50",
      "End": "128",
      "Str": "0",
      "Fre": "3216",
      "Opt": "CONSTANT",
      "Pha": "7",
      "VSR": "-1",
      "WFT": "-1",
      "Wav": "PWM"
    },
    "SequenceItem10": {
      "Pin0": "8",
      "Pin1": "8",
      "Pin2": "8",
      "Amp": "1",
      "CT": "50",
      "End": "128",
      "Str": "0",
      "Fre": "3797",
      "Opt": "CONSTANT",
      "Pha": "1",
      "VSR": "-1",
      "WFT": "-1",
      "Wav": "PWM"
    },
    "SequenceItem11": {
      "Pin0": "11",
      "Amp": "0",
      "CT": "0",
      "End": "128",
      "Str": "0",
      "Fre": "5000",
      "Opt": "RECORD",
      "Pha": "0",
      "VSR": "-1",
      "WFT": "-1",
      "Wav": "emNULL"
    }
  },
  "Results": {
    "Case 0": " TESTCASE 0  False,True =>True  False FAIL",
    "Case 1": " TESTCASE 1  False,True =>True  False FAIL",
    "Case 2": " TESTCASE 2  False,False=>True  False FAIL",
    "Case 3": " TESTCASE 3  True ,True =>False False PASS",
    "Case 4": " TESTCASE 4  False,False=>True  False FAIL",
    "Case 5": " TESTCASE 5  True ,True =>False False PASS",
    "Case 6": " TESTCASE 6  True ,True =>False False PASS",
    "Case 7": " TESTCASE 7  False,False=>True  False FAIL",
    "Case 8": " TESTCASE 8  True ,False=>True  False FAIL",
    "Case 9": " TESTCASE 9  False,False=>True  False FAIL",
    "Case 10": " TESTCASE 10 True ,False=>True  False FAIL",
    "Case 11": " TESTCASE 11 False,True =>True  False FAIL",
    "Case 12": " TESTCASE 12 True ,False=>True  False FAIL",
    "Case 13": " TESTCASE 13 False,True =>True  False FAIL",
    "Case 14": " TESTCASE 14 True ,True =>False False PASS",
    "Case 15": " TESTCASE 15 True ,False=>True  False FAIL"
  },
  "Fitness": {
    "Score": "0.25",
    "Evaluation index": "5"
  }
}
