NASCENCE/mecobo/EMServer/bin/LogServer/Gates_20140803_103645/20140803_103649350_CONFIG.txt

{
  "Seq": {
    "SI0": {
      "PC": "1",
      "Pin0": "7",
      "Amp": "1",
      "CT": "0",
      "End": "128",
      "Str": "0",
      "Fre": "0",
      "Opt": "CONSTANT",
      "Pha": "0",
      "VSR": "-1",
      "WFT": "-1",
      "Wav": "PWM"
    },
    "SI1": {
      "PC": "1",
      "Pin0": "3",
      "Amp": "0",
      "CT": "0",
      "End": "128",
      "Str": "0",
      "Fre": "0",
      "Opt": "CONSTANT",
      "Pha": "0",
      "VSR": "-1",
      "WFT": "-1",
      "Wav": "PWM"
    },
    "SI2": {
      "PC": "1",
      "Pin0": "7",
      "Amp": "0",
      "CT": "0",
      "End": "129",
      "Str": "128",
      "Fre": "0",
      "Opt": "emNULL",
      "Pha": "0",
      "VSR": "-1",
      "WFT": "-1",
      "Wav": "emNULL"
    },
    "SI3": {
      "PC": "1",
      "Pin0": "5",
      "Amp": "0",
      "CT": "50",
      "End": "128",
      "Str": "0",
      "Fre": "1571",
      "Opt": "CONSTANT",
      "Pha": "6",
      "VSR": "-1",
      "WFT": "-1",
      "Wav": "PWM"
    },
    "SI4": {
      "PC": "1",
      "Pin0": "11",
      "Amp": "1",
      "CT": "50",
      "End": "128",
      "Str": "0",
      "Fre": "7215",
      "Opt": "CONSTANT",
      "Pha": "9",
      "VSR": "-1",
      "WFT": "-1",
      "Wav": "PWM"
    },
    "SI5": {
      "PC": "1",
      "Pin0": "1",
      "Amp": "1",
      "CT": "50",
      "End": "128",
      "Str": "0",
      "Fre": "9731",
      "Opt": "CONSTANT",
      "Pha": "3",
      "VSR": "-1",
      "WFT": "-1",
      "Wav": "PWM"
    },
    "SI6": {
      "PC": "1",
      "Pin0": "8",
      "Amp": "1",
      "CT": "50",
      "End": "128",
      "Str": "0",
      "Fre": "4286",
      "Opt": "CONSTANT",
      "Pha": "5",
      "VSR": "-1",
      "WFT": "-1",
      "Wav": "PWM"
    },
    "SI7": {
      "PC": "1",
      "Pin0": "0",
      "Amp": "0",
      "CT": "50",
      "End": "128",
      "Str": "0",
      "Fre": "9390",
      "Opt": "CONSTANT",
      "Pha": "9",
      "VSR": "-1",
      "WFT": "-1",
      "Wav": "PWM"
    },
    "SI8": {
      "PC": "1",
      "Pin0": "6",
      "Amp": "1",
      "CT": "50",
      "End": "128",
      "Str": "0",
      "Fre": "4928",
      "Opt": "CONSTANT",
      "Pha": "5",
      "VSR": "-1",
      "WFT": "-1",
      "Wav": "PWM"
    },
    "SI9": {
      "PC": "1",
      "Pin0": "2",
      "Amp": "1",
      "CT": "50",
      "End": "128",
      "Str": "0",
      "Fre": "7197",
      "Opt": "CONSTANT",
      "Pha": "5",
      "VSR": "-1",
      "WFT": "-1",
      "Wav": "PWM"
    },
    "SI10": {
      "PC": "1",
      "Pin0": "10",
      "Amp": "0",
      "CT": "50",
      "End": "128",
      "Str": "0",
      "Fre": "4635",
      "Opt": "CONSTANT",
      "Pha": "8",
      "VSR": "-1",
      "WFT": "-1",
      "Wav": "PWM"
    },
    "SI11": {
      "PC": "1",
      "Pin0": "4",
      "Amp": "0",
      "CT": "0",
      "End": "128",
      "Str": "0",
      "Fre": "5000",
      "Opt": "RECORD",
      "Pha": "0",
      "VSR": "-1",
      "WFT": "-1",
      "Wav": "emNULL"
    }
  },
  "Results": {
    "Case 0": " TESTCASE 0  True ,False=>True  False FAIL",
    "Case 1": " TESTCASE 1  False,True =>True  False FAIL",
    "Case 2": " TESTCASE 2  False,False=>True  False FAIL",
    "Case 3": " TESTCASE 3  False,True =>True  False FAIL",
    "Case 4": " TESTCASE 4  True ,False=>True  False FAIL",
    "Case 5": " TESTCASE 5  True ,False=>True  False FAIL",
    "Case 6": " TESTCASE 6  True ,True =>False False PASS",
    "Case 7": " TESTCASE 7  False,False=>True  False FAIL",
    "Case 8": " TESTCASE 8  False,True =>True  False FAIL",
    "Case 9": " TESTCASE 9  True ,True =>False False PASS",
    "Case 10": " TESTCASE 10 True ,True =>False False PASS",
    "Case 11": " TESTCASE 11 True ,True =>False False PASS",
    "Case 12": " TESTCASE 12 False,False=>True  False FAIL",
    "Case 13": " TESTCASE 13 False,True =>True  False FAIL",
    "Case 14": " TESTCASE 14 False,False=>True  False FAIL",
    "Case 15": " TESTCASE 15 True ,False=>True  False FAIL"
  },
  "Fitness": {
    "Score": "0.25",
    "Evaluation index": "0"
  }
}
