NASCENCE/mecobo/uc/adc.c

#include "adc.h"
#include "mecobo.h"
#include "em_usb.h"
#include <inttypes.h>

void setupADC()
{
    //uint16_t CTRL = 0x8000;   //100 .
    //ad[0x01] = 0; //overflow
    //ad[0x02] = 1; //divide

    //Set up mode for all channels (we use 8 single ended inputs.)
    for(uint32_t i = 0; i < 8; i++) {
        uint32_t ctrlWord = 0x18014 | (i << 10);
        command(0, AD_CHANNELS_START, AD_REG_PROGRAM, ctrlWord);
    }

    command(0, AD_CHANNELS_START, AD_REG_PROGRAM, 0x1AAA0);
    command(0, AD_CHANNELS_START, AD_REG_PROGRAM, 0x1CAA0);

    //Range register 1
    //uint16_t data = 0;
    //ad[0x04] = lol; //range register written to +-5V on all channels for chans 0 to 4
    //while((data = ad[0x0B]) != lol) {printf("a:%x\n", data);}  //check if busy, if not, go.
    //printf("setup finally: %x\n", data);
    //Range register 2
    //ad[0x04] = 0xCAA0; //range register written to +-5V on all channels for chans 4 to 7
    //while((data = ad[0x0B]) != 0xCAA0) {printf("c:%x\n", data);}  //check if busy, if not, go.
    //printf("setup finally: %x\n", data);
}
