NASCENCE/mecobo/fpga/sample_collector.v

/* 
* This module is the interface for sampling storage.
*
* It has room for 10 adresses which point to
* the various units in the system. By writing the POSITION to address 0,
* the collection_channels register will be updated with this unit and it will
* be included in the collection state machine.
* 
* A read from the unit is forwarded directly to the sample FIFO.
*
* When reading from this unit, a sample will be collected. If no reading is done,
* the unit will simply keep filling the memory until it is full.
*
*
*/


`define WITH_DB
module sample_collector (
    input clk,
    input rst,

    /*command bus */
    input [15:0] addr,
    input [31:0] cmd_data_in,
    input cs,
    input wr,

    output reg output_sample,
    output reg [7:0] channel_select,

    /*Memory writing interface exposed to the mem-subsystem of the controllers. */
    input [31:0] sample_data,
    input global_clock_running,
    /*This interface is exposed to allow reading out data from FIFO */
    input sample_fifo_rd_en,
    output [15:0] sample_data_out,
    output sample_fifo_empty,
    output sample_fifo_almost_empty,
    output sample_fifo_full,
    output sample_fifo_almost_full,
    output [15:0] sample_fifo_data_count
);

parameter POSITION = 242;
parameter MAX_COLLECTION_UNITS = 64;

localparam ADDR_NEXT_SAMPLE = 1;
localparam ADDR_NUM_SAMPLES = 2;
localparam ADDR_READ_ADDR = 3;
localparam ADDR_NEW_UNIT = 4;
localparam ADDR_LOCAL_COMMAND = 5;
localparam ADDR_NUM_UNITS = 6;
localparam ADDR_DEBUG = 10;

localparam
CMD_START_SAMPLING = 1,
CMD_STOP_SAMPLING = 2,
CMD_RES_SAMPLE_FIFO = 3,
CMD_RESET = 5;


/*The collection unit registers hold the position of the unit to enable.
*/
reg [7:0] collection_channels[0:MAX_COLLECTION_UNITS];
reg [5:0] num_units = 0;  //6 bits for indexing.

/*reg [18:0] num_samples = 0; 
*/

reg [31:0] command;
/*will start out as 0. */

wire controller_enable;
assign controller_enable = (cs & (addr[15:8] == POSITION));


/*When a read to the special read register is done,
memory_bottom_addr is incremented and the next value is fetched from
memory automatically such that it is available when the next read request comes.

state machine that runs across all collection_channels and fetches a sample,
and then stores it in a fifo
*/

parameter idle          = 5'b00001;
parameter store         = 5'b00010;
parameter increment     = 5'b00100;
parameter fetch         = 5'b01000;
parameter fetch_wait    = 5'b10000;
reg [4:0] state, nextState;

/* control path signals */
reg output_sample_signal;
reg inc_curr_id_idx;
reg fifo_write_enable;
reg en_read;
reg res_cmd_reg;
reg res_sampling;
reg res_fifo;
wire wr_transaction_done;

reg [31:0] last_fetched [0:MAX_COLLECTION_UNITS];

integer mi;
initial begin 
    state = idle;
    for (mi = 0; mi < MAX_COLLECTION_UNITS; mi = mi + 1)  begin
        collection_channels[mi] = 255;
        last_fetched[mi] = 0;
    end
end


reg [5:0] current_id_idx = 0;


always @ (posedge clk) begin
    if (rst) state <= idle;
    else state <= nextState;
end

always @ (*) begin
    output_sample_signal = 0;
    inc_curr_id_idx = 0;
    fifo_write_enable = 0;
    res_cmd_reg = 0;
    res_sampling = 0;
    res_fifo = 0;
    nextState = 5'bXXXXX;

    case (state)
        idle: begin
            nextState = idle;
            if(command == CMD_START_SAMPLING) begin
                if(global_clock_running) begin
                    res_cmd_reg = 1'b1;
                    nextState = fetch;
                end
            end else if (command == CMD_RESET) begin
                res_sampling = 1'b1;
            end else if (command == CMD_RES_SAMPLE_FIFO) begin
                res_fifo = 1'b1;
            end 
        end

        /*instruct adc to output new sample data */
        fetch: begin
            output_sample_signal = 1'b1;  //on next flank, output sample will go high (registered)
            nextState = fetch_wait;
        end

        /*output sample goes high here, the addressed unit will on the next
        * flank and output it's sample_data 
        *
        * we wait here to let the data arrive (timing constraints...)
        * */

        fetch_wait: begin
            nextState = store;
        end

        /* one flank later, the data should be available on the input pins here.
        * we store it only if it's not the same as the previosuly fetched data.
        *
        * this comparison can be quite long, and potentially we could 
        * add a cycle here to only capture the sample_data no matter what
        * and then compare it one cycle later.
        * */
        store: begin
            if (last_fetched[current_id_idx] != sample_data) begin
                fifo_write_enable = 1'b1;
            end
            nextState = increment; 
        end

        /*increment index counters for fetching from more units. */
        increment: begin
            inc_curr_id_idx = 1'b1;

            nextState = fetch;
            if(command == CMD_RESET)  begin
                res_sampling = 1'b1;
                nextState = idle;
            end else if (command == CMD_STOP_SAMPLING) begin
                res_cmd_reg = 1'b1;
                nextState = idle;
            end
        end

    endcase
end


/* DATA PATH */

integer mj;
always @ (posedge clk) begin

    if (rst) begin
        for (mj = 0; mj < MAX_COLLECTION_UNITS; mj = mj + 1)  begin
            collection_channels[mj] <= 255; /* no such channel: special. */
            last_fetched[mj] <= 0;
        end
        command <= 0;
        num_units <= 0;
        channel_select <= 0;
        output_sample <= 0;

    end else begin

        if (res_cmd_reg) begin  //this happens when we're leaving the idle state and are going to do stuff
            command <= 0;
            //else the res_sampling happens and we should reset everything.
        end else if (res_sampling) begin
            command <= 0;
            for (mj = 0; mj < MAX_COLLECTION_UNITS; mj = mj + 1)  begin
                collection_channels[mj] <= 255; /* no such channel: special. */
                last_fetched[mj] <= 0;
            end
            command <= 0;
            num_units <= 0;
            current_id_idx <= 0;
        end else begin
            if (controller_enable & wr) begin
                if (addr[7:0] == ADDR_NEW_UNIT) begin
                    collection_channels[num_units] <= cmd_data_in[7:0];
                end

                if (addr[7:0] == ADDR_LOCAL_COMMAND) begin
                    command <= cmd_data_in;
                end

                if (addr[7:0] == ADDR_NUM_UNITS) begin
                    num_units <= cmd_data_in[5:0];
                end
            end       

            //Write to last fetched to compare against old value fetched from same
            //unit
            if(fifo_write_enable) 
                last_fetched[current_id_idx] <= sample_data;
            //Increment number of units when add unit command comes in
            //if ((addr[7:0] == ADDR_NEW_UNIT) & wr_transaction_done) 
            //    num_units <= num_units + 1;

            /*only increment mod num_units-1 (0-indexed) */
            if (inc_curr_id_idx) begin
                if((current_id_idx == (num_units-1)) & (num_units != 0)) 
                    current_id_idx <= 0;
                else
                    current_id_idx <= (current_id_idx + 1);
            end

        end 
      
        if(output_sample_signal) begin
            channel_select <= collection_channels[current_id_idx];
            output_sample <= 1'b1;
        end else begin
            channel_select <= 0;
            output_sample <= 1'b0;
        end

    end //res_cmd
end



/* FIFO */
wire [15:0] fifo_data_in;


`ifdef WITH_DB
    /* 3 bits of ID, 13 bits of sample data*/
    assign fifo_data_in = {current_id_idx[2:0], sample_data[12:0]}; /*last_fetched[current_id_idx][15:0]; */
`else
    assign fifo_data_in = sample_data[15:0];
`endif

sample_fifo sample_fifo_0 (
    .clk(clk),
    .rst(res_fifo | res_sampling | rst),
    .din(fifo_data_in),
    .wr_en(fifo_write_enable),
    .rd_en(sample_fifo_rd_en),
    .dout(sample_data_out),
    .full(sample_fifo_full),
    .almost_full(sample_fifo_almost_full),
    .wr_ack(),
    .overflow(),
    .underflow(),
    .empty(sample_fifo_empty),
    .almost_empty(sample_fifo_almost_empty),
    .valid(),
    .data_count(sample_fifo_data_count)
);

            //-----------------------------------------------------------------------------------
            //rd falling edge detection to see if a transaction has finished

            reg wr_d = 0;
            reg wr_dd = 0;

            always @ (posedge clk) begin
                if(rst) begin
                    wr_d <= 1'b0;
                    wr_dd <= 1'b0;
                end else begin
                    wr_d <= wr & controller_enable;
                    wr_dd <= wr_d;
                end 
            end

            //if r_dd is high and rd_d is low, we have seen a falling edge.
            assign wr_transaction_done = (~wr_d) & (wr_dd);


endmodule
